lnbits/tpos-receipt-printer/firmware/src/config.h

#ifndef config_h
#define config_h

const bool includeQuotes = true; // Add Satoshi quotes to the receipt
const char* companyName = "LNbits Shop";
const char* ssid = "Maddox Guest";
const char* password = "MadGuest1";
const char* host = "legend.lnbits.com";
const char* walletId = "845ad088a1604d96ba039b7d6efe87ab";

const bool printToSerialOnly = false; // Set to true to only print to serial monitor for debugging

#endif
